RENOX-DATABASE/steering_wheel_cad/Spring 1.SLDPRT

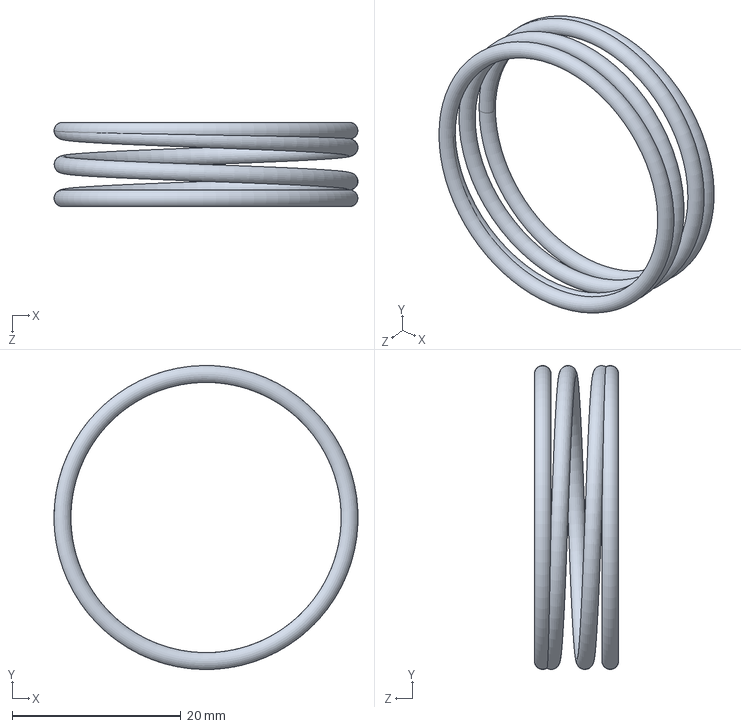
[picture p15: CAD file, 2023-03-19]
Spring 1.SLDPRT
36.0 x 36.0 x 10.0 mm
