RENOX-DATABASE/steering_wheel_cad/RF018 Spacer for Shifter Circle[Φ5 3].SLDPRT

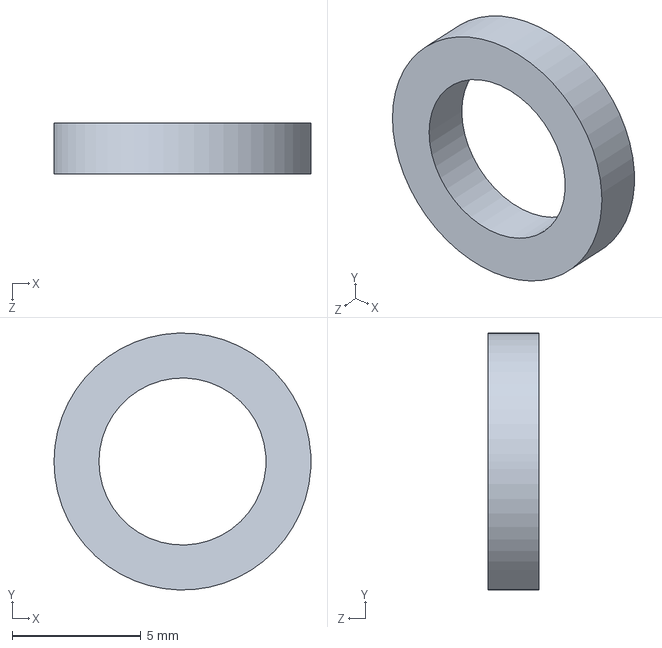
[picture p16: CAD file, 2023-03-19]
RF018 Spacer for Shifter Circle[Φ5 3].SLDPRT
10.0 x 10.00 x 2.00 mm
