RENOX-DATABASE/steering_wheel_cad/1-2.SLDPRT

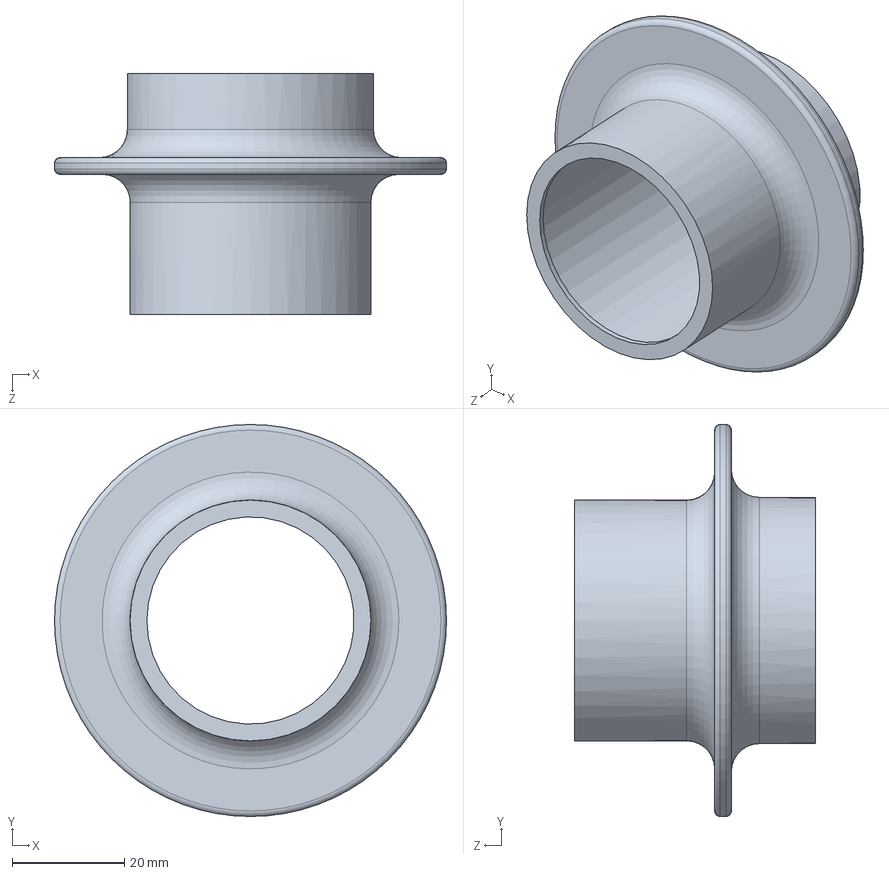
[picture p17: CAD file, 2023-03-19]
1-2.SLDPRT
70.0 x 70.0 x 43.0 mm
