RENOX-DATABASE/steering_wheel_cad/RF019 AC kai Display.SLDPRT

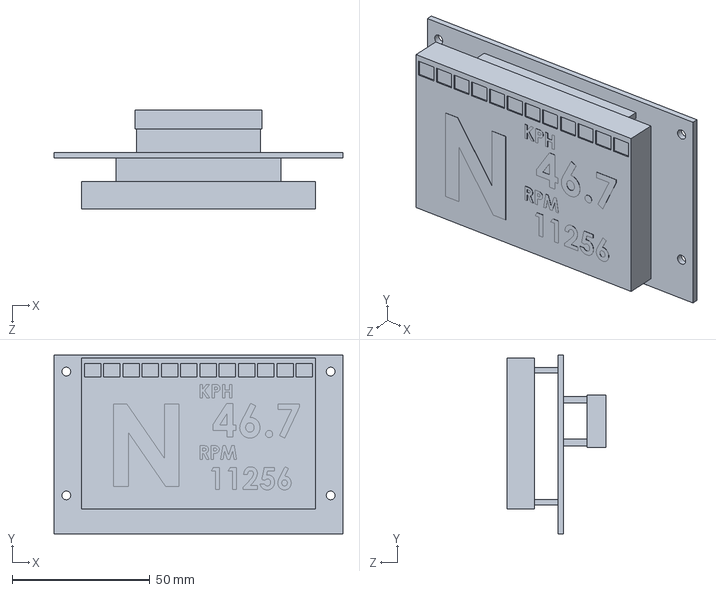
[picture p18: CAD file, 2023-03-19]
RF019 AC kai Display.SLDPRT
105.0 x 65.0 x 36.1 mm
