RENOX-DATABASE/steering_wheel_cad/1-5.SLDPRT

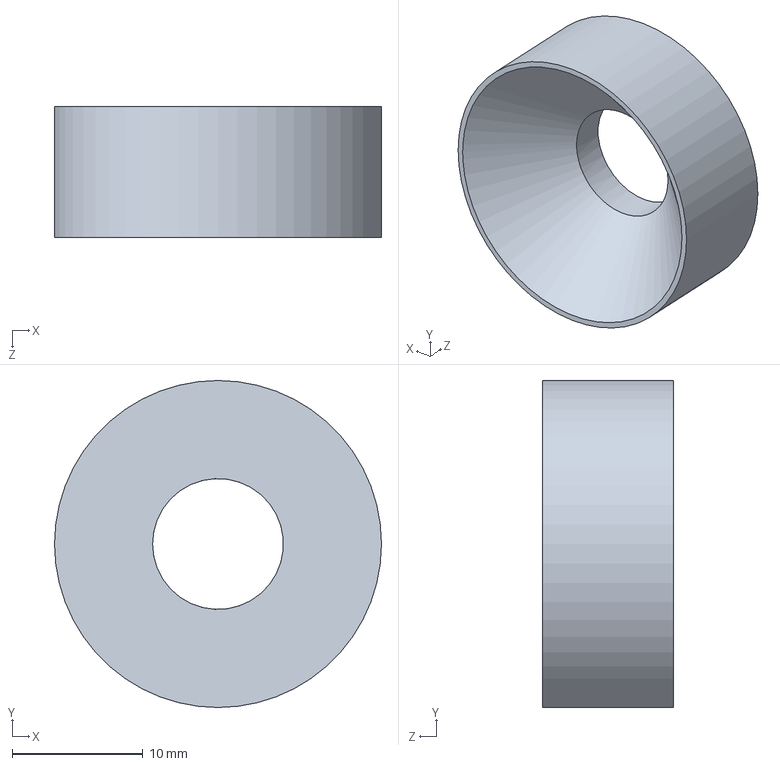
[picture p19: CAD file, 2023-03-19]
1-5.SLDPRT
25.0 x 25.0 x 10.0 mm
