RENOX-DATABASE/steering_wheel_cad/Spring 2.SLDPRT

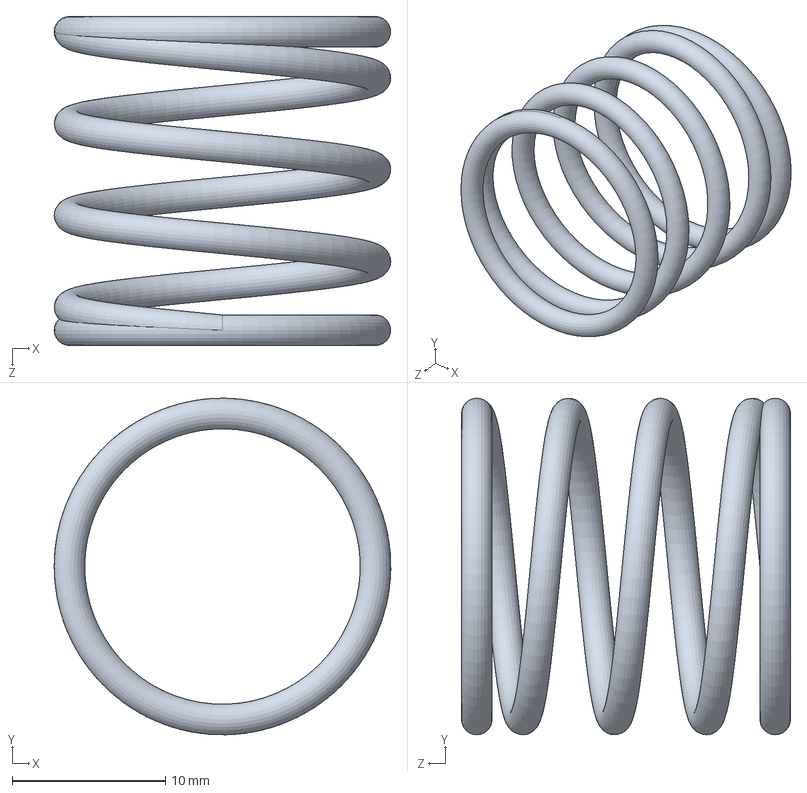
[picture p20: CAD file, 2023-03-19]
Spring 2.SLDPRT
22.0 x 22.0 x 21.5 mm
