RENOX-DATABASE/steering_wheel_cad/RF019 SWCP kai.SLDPRT

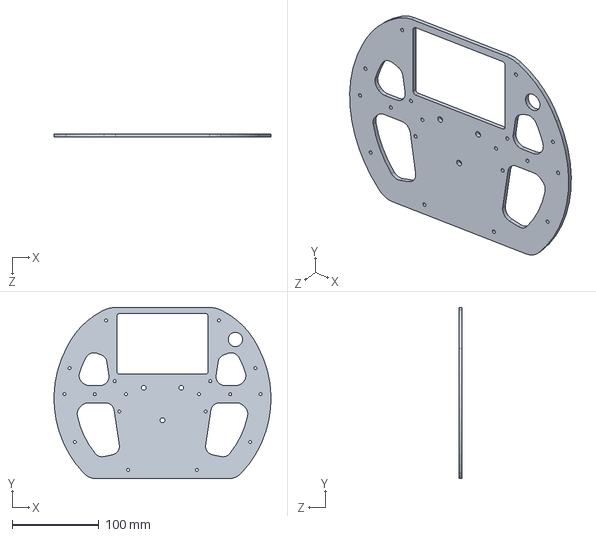
[picture p21: CAD file, 2023-03-19]
RF019 SWCP kai.SLDPRT
249.9 x 197.3 x 4.00 mm
