RENOX-DATABASE/steering_wheel_cad/1-3.SLDPRT

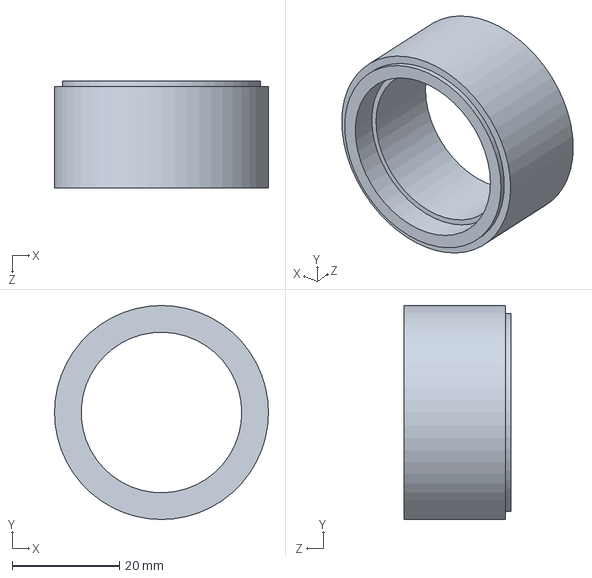
[picture p22: CAD file, 2023-03-19]
1-3.SLDPRT
40.0 x 40.0 x 20.0 mm
