RENOX-DATABASE/steering_wheel_cad/RF019 SWB kai B3.SLDPRT

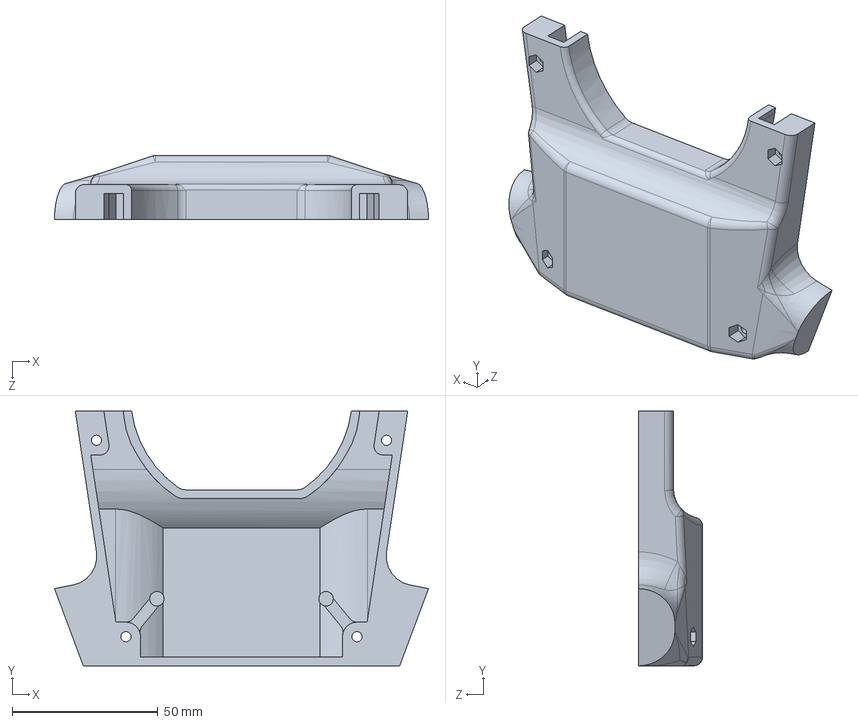
[picture p23: CAD file, 2023-03-19]
RF019 SWB kai B3.SLDPRT
128.2 x 87.3 x 22.0 mm
