RENOX-DATABASE/steering_wheel_cad/RF019 SWG kai RF.SLDPRT

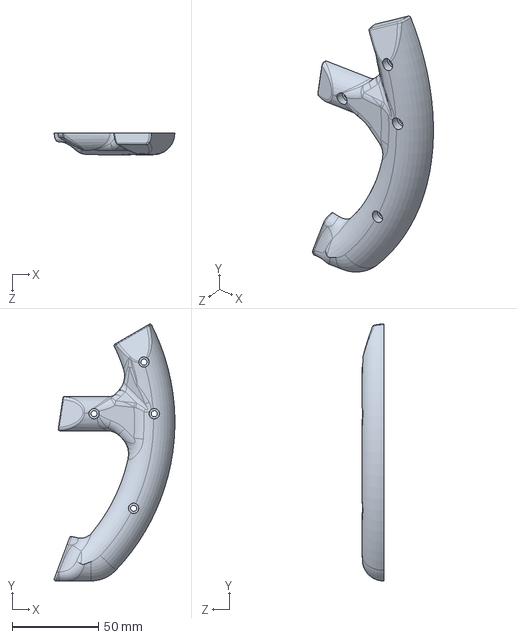
[picture p24: CAD file, 2023-03-19]
RF019 SWG kai RF.SLDPRT
70.2 x 149.4 x 12.5 mm
