RENOX-DATABASE/steering_wheel_cad/RF019 SC kai.SLDPRT

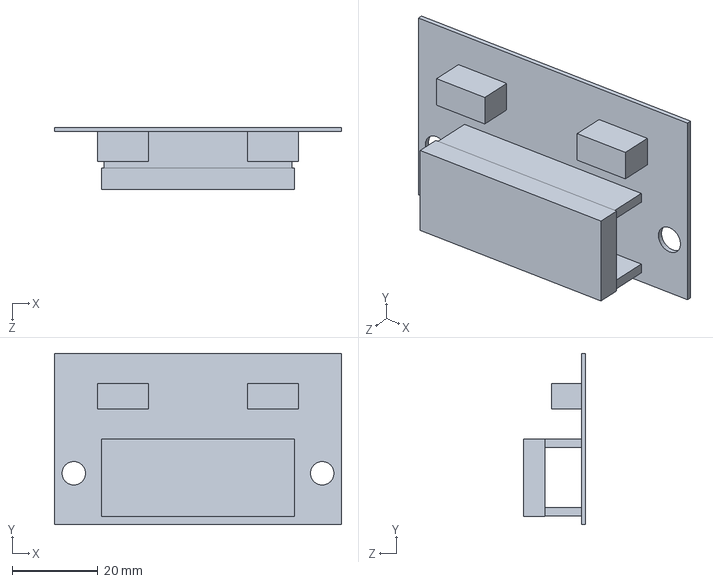
[picture p25: CAD file, 2023-03-19]
RF019 SC kai.SLDPRT
67.0 x 40.0 x 14.5 mm
