RENOX-DATABASE/steering_wheel_cad/1-4.SLDPRT

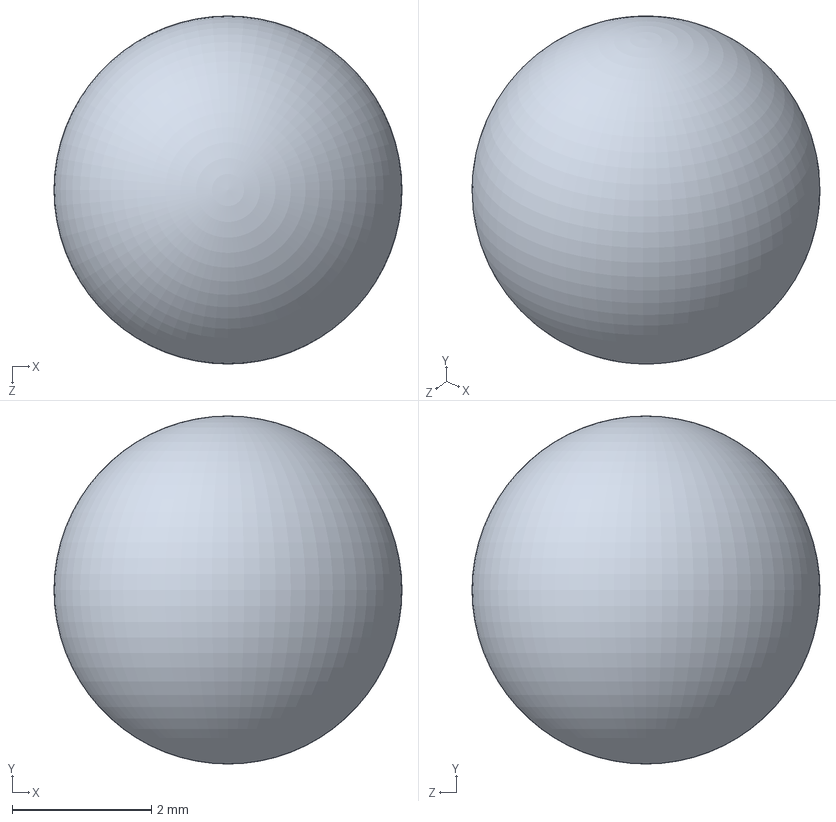
[picture p26: CAD file, 2023-03-19]
1-4.SLDPRT
5.00 x 5.00 x 5.00 mm
