RENOX-DATABASE/steering_wheel_cad/RF018 Paddle Shift Adapt Switch.SLDPRT

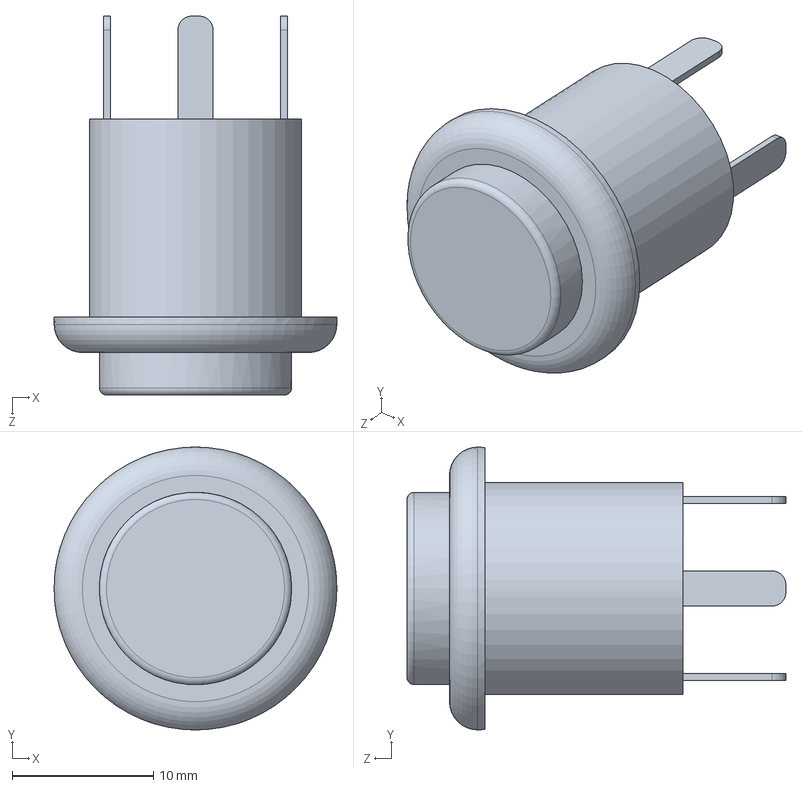
[picture p27: CAD file, 2023-03-19]
RF018 Paddle Shift Adapt Switch.SLDPRT
20.0 x 20.0 x 26.8 mm
