RENOX-DATABASE/steering_wheel_cad/RF019 SWB kai B1.SLDPRT

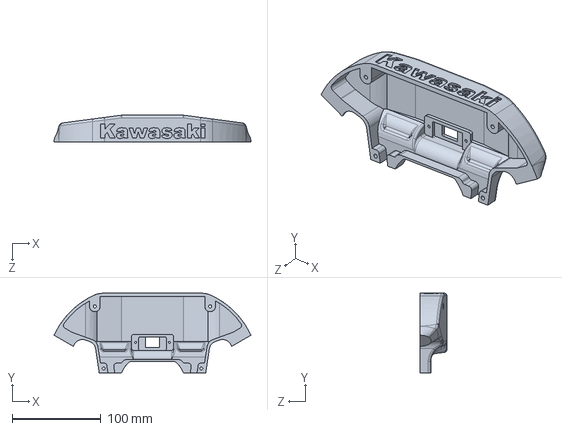
[picture p28: CAD file, 2023-03-19]
RF019 SWB kai B1.SLDPRT
221.9 x 90.0 x 30.0 mm
