RENOX-DATABASE/steering_wheel_cad/RF018 Spacer for SWMB[M3 9].SLDPRT

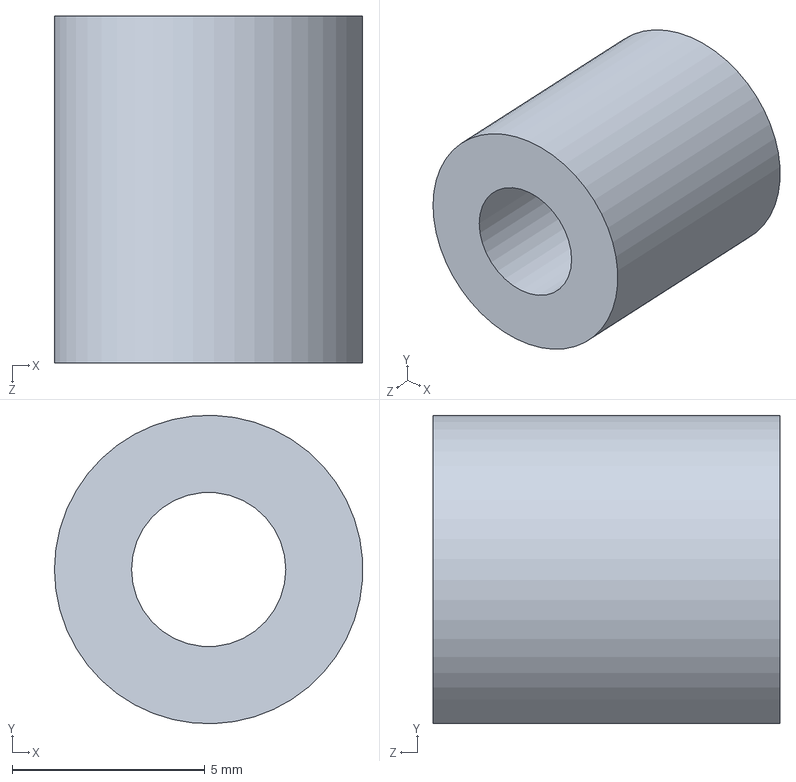
[picture p29: CAD file, 2023-03-19]
RF018 Spacer for SWMB[M3 9].SLDPRT
7.99 x 8.00 x 9.00 mm
