RENOX-DATABASE/steering_wheel_cad/M2 Nat.SLDPRT

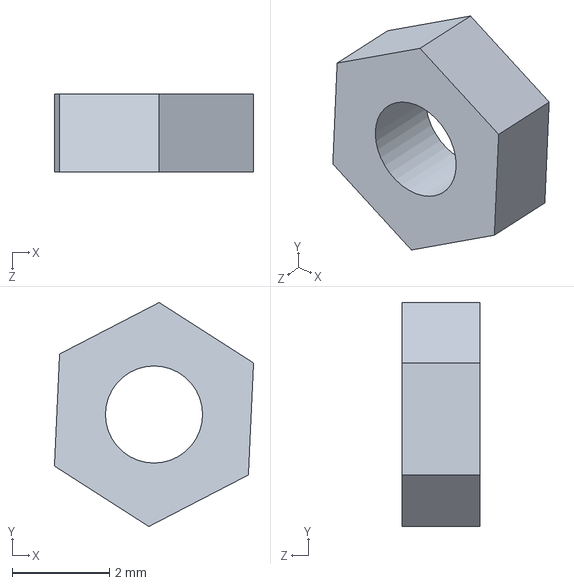
[picture p30: CAD file, 2023-03-19]
M2 Nat.SLDPRT
4.10 x 4.61 x 1.60 mm
